koert/midi-controller/design/pressure-button-matrix/pressure-button-4x4-double_etch_silk_top.pdf

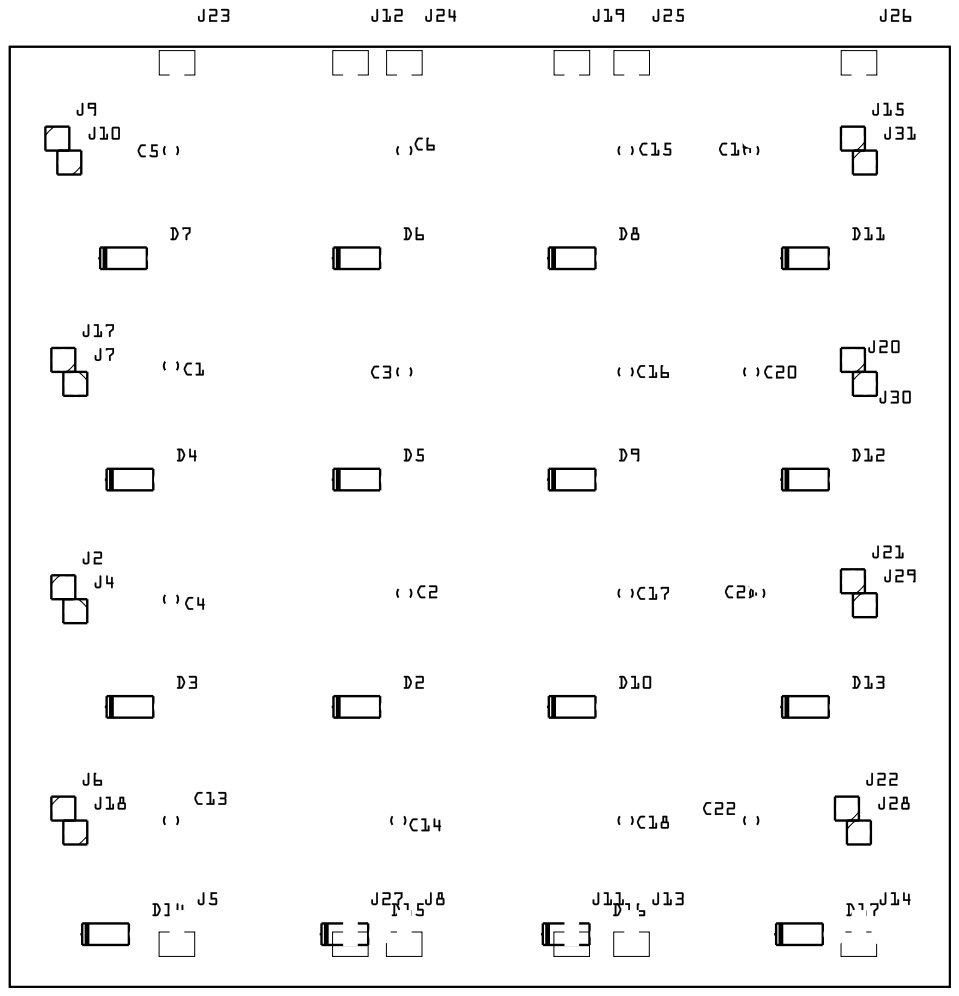
[picture p12: page 1]
