koert/midi-controller/design/pressure-button-matrix/pressure-button-4x4-double_etch_silk_top_mirror.pdf

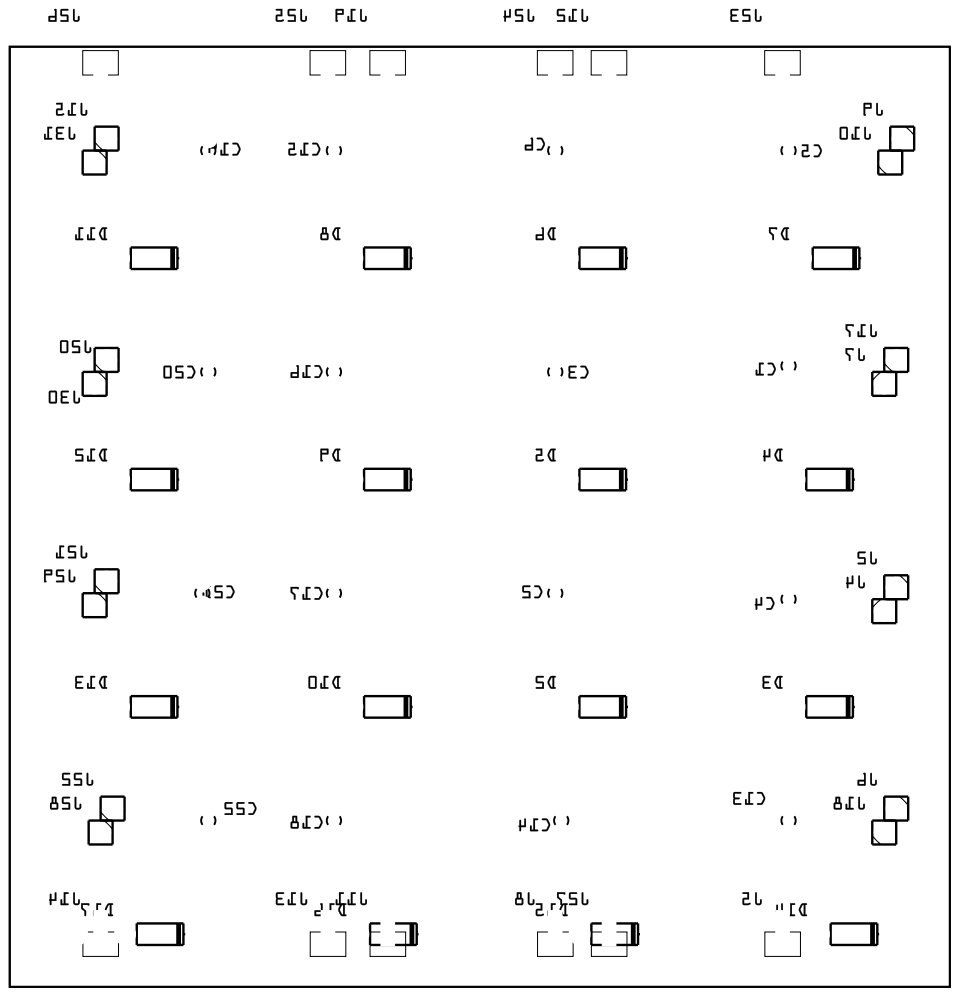
[picture p13: page 1]
