koert/midi-controller/design/controller-pcb/midi-controller-teensy_etch_copper_bottom.pdf

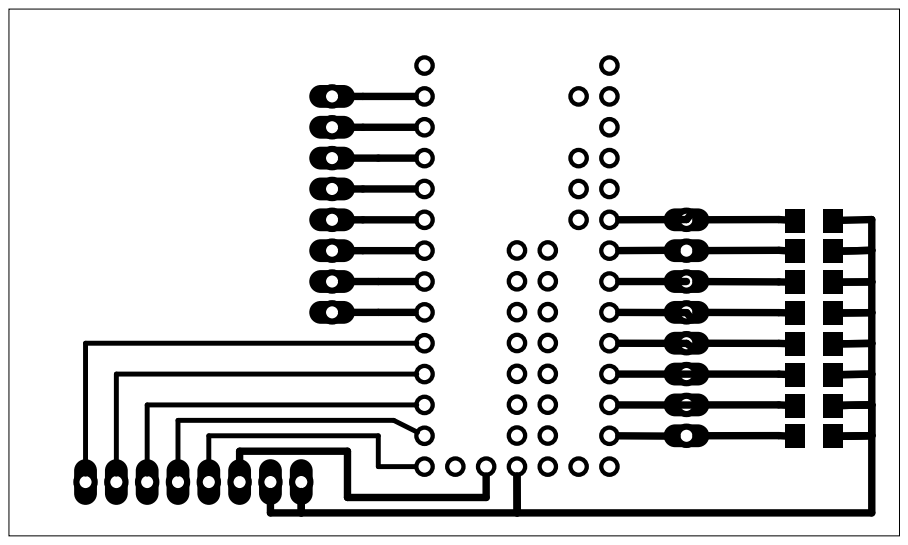
[picture p14: page 1]
