koert/midi-controller/design/controller-pcb/midi-controller-teensy_etch_copper_bottom_mirror.pdf

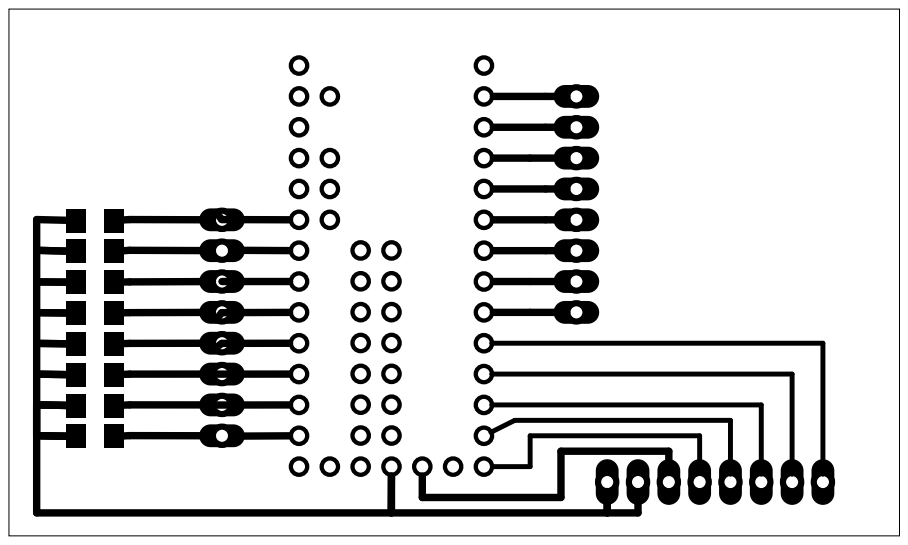
[picture p15: page 1]
