koert/midi-controller/design/controller-pcb/midi-controller-teensy_etch_copper_top.pdf

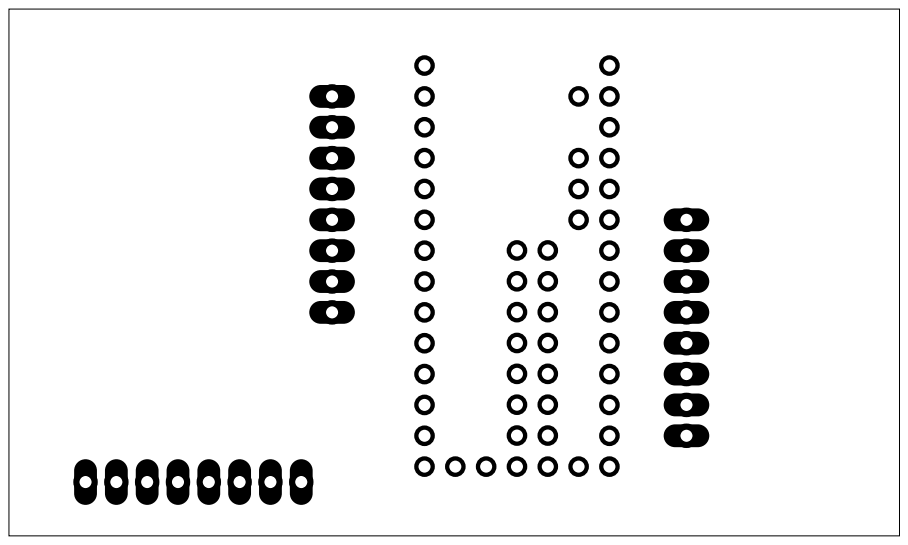
[picture p16: page 1]
