koert/midi-controller/design/controller-pcb/midi-controller-teensy_etch_copper_top_mirror.pdf

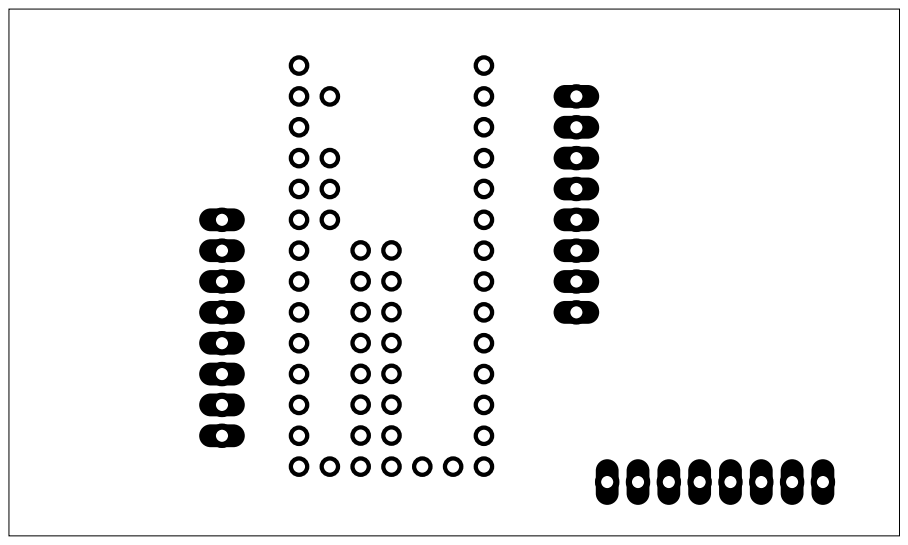
[picture p17: page 1]
