koert/midi-controller/design/controller-pcb/midi-controller-teensy_etch_mask_bottom.pdf

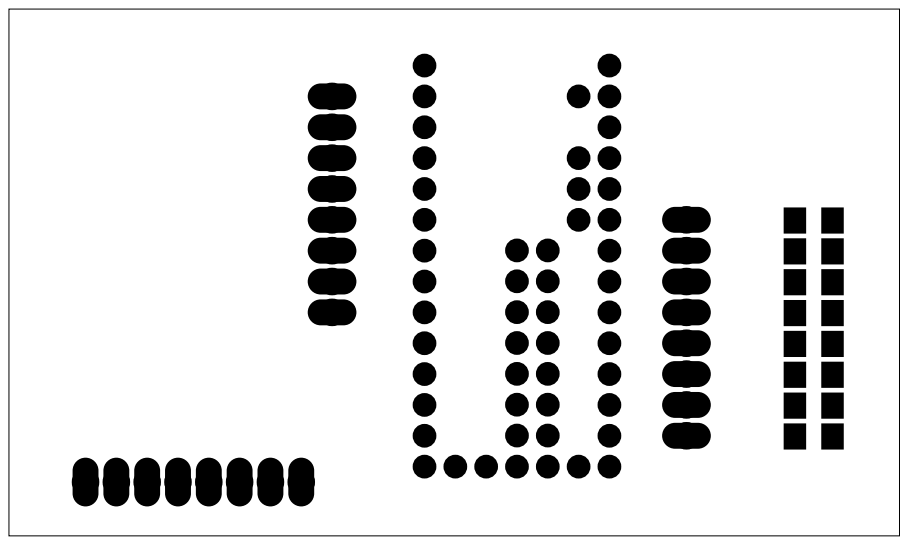
[picture p18: page 1]
