koert/midi-controller/design/controller-pcb/midi-controller-teensy_etch_mask_bottom_mirror.pdf

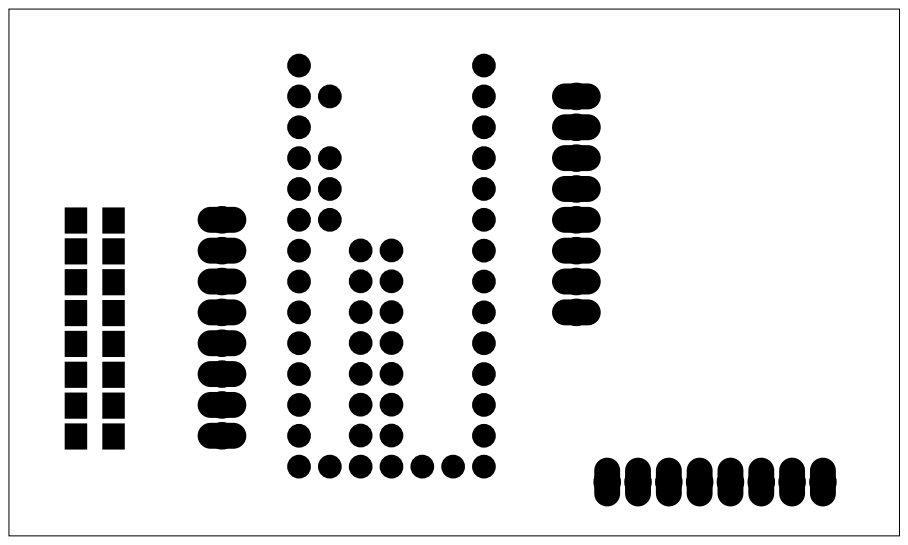
[picture p19: page 1]
