koert/midi-controller/design/controller-pcb/midi-controller-teensy_etch_mask_top.pdf

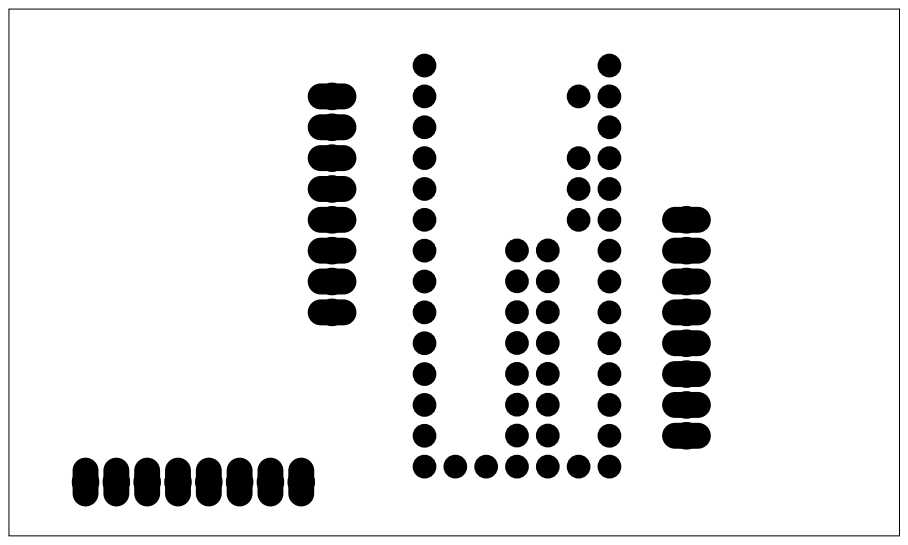
[picture p20: page 1]
