koert/midi-controller/design/controller-pcb/midi-controller-teensy_etch_mask_top_mirror.pdf

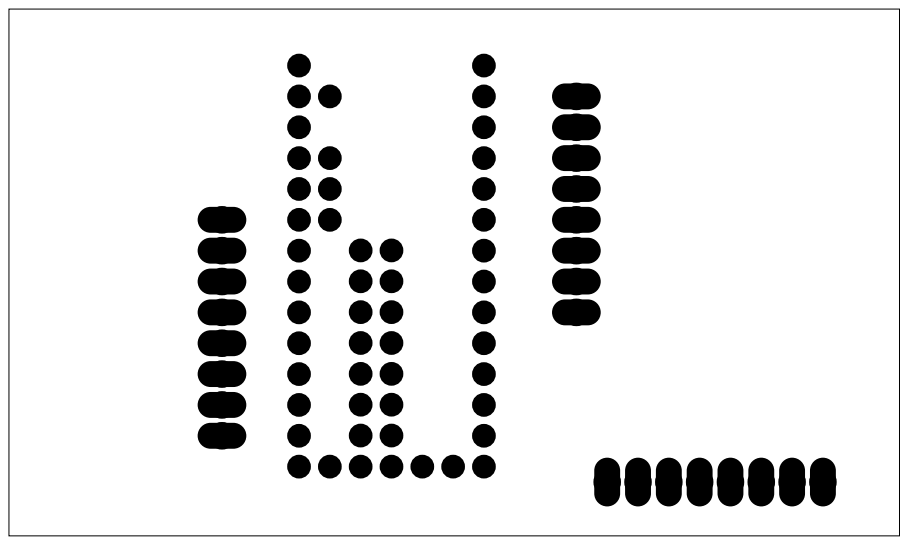
[picture p21: page 1]
