koert/midi-controller/design/controller-pcb/midi-controller-teensy_etch_silk_top.pdf

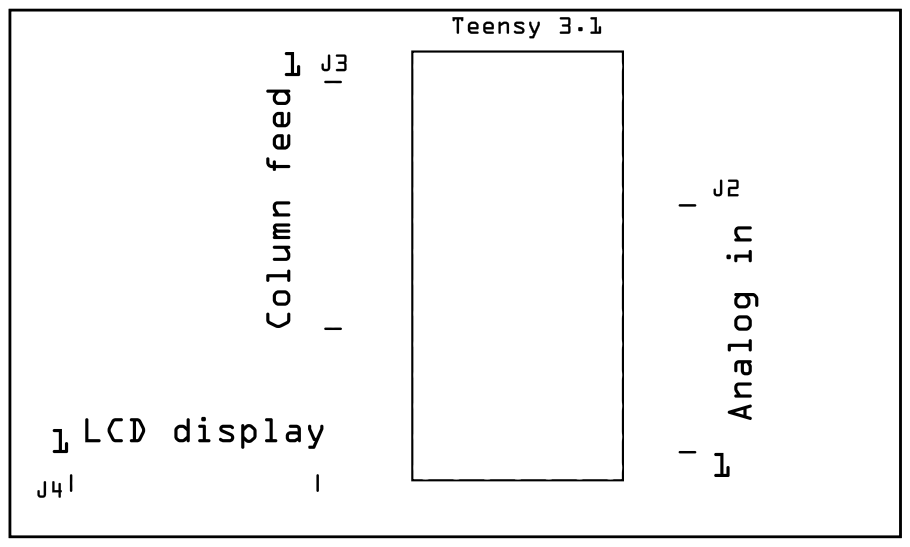
[picture p22: page 1]
