koert/midi-controller/design/controller-pcb/midi-controller-teensy_etch_silk_top_mirror.pdf

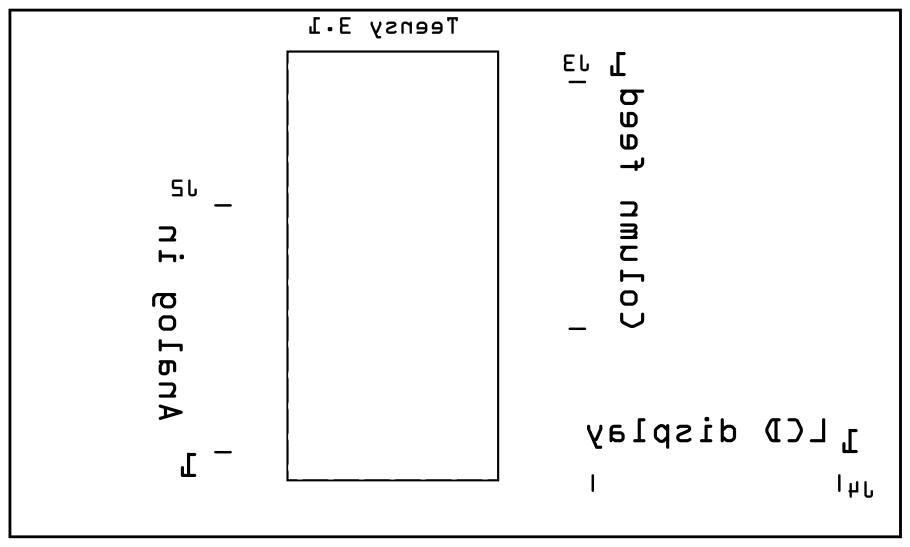
[picture p23: page 1]
